AtomicAlbatross/esPass/Words.h

static const String wordList[] PROGMEM = {"Smoothly",
"Clearly",
"Strongly",
"Abnormally",
"Generously",
"Specifically",
"Upbeat",
"Scarcely",
"Fully",
"Frantically",
"Kindheartedly",
"Deftly",
"Grass",
"Stimulating",
"Thoughtful",
"Red",
"Elastic",
"Dare",
"Extra-large",
"Adhesive",
"Intelligent",
"Repeat",
"Voyage",
"Wall",
"Preserve",
"Territory",
"Story",
"Agonizing",
"Swing",
"Chunky",
"Waggish",
"Grubby",
"Cushion",
"Winter",
"Fowl",
"Shoes",
"Value",
"Airplane",
"Thread",
"Zipper",
"Mother",
"Quicksand",
"Roll",
"Legs",
"Treatment",
"Farm",
"Pocket",
"Yarn",
"Brake",
"Circle",
"Horn",
"Skate",
"Liquid",
"Join",
"Apparatus",
"Bomb",
"Zephyr",
"Price",
"Pot",
"Error",
"Hammer",
"Sheep",
"Roof",
"Memory",
"Minister",
"Jelly",
"Zebra",
"Cherry",
"Rice",
"Prose",
"Clam",
"Question",
"Desire",
"Aftermath",
"Adjustment",
"Cheese",
"Jellyfish",
"Seed",
"Push",
"Top",
"Record",
"Robin",
"Receipt",
"Rail",
"Stew",
"Stove",
"Act",
"Ants",
"Visitor",
"Pies",
"Note",
"Mint",
"Hydrant",
"Part",
"Attack",
"Beef",
"Middle",
"Steam",
"Lip",
"Shape",
"Money",
"Experience",
"Achiever",
"Lake",
"Scarf",
"Yam",
"Fire",
"Limit",
"Daughter",
"Night",
"Shake",
"Rain",
"Birth",
"Boot",
"Meeting",
"Believe",
"Flock",
"Animal",
"Design",
"Soda",
"Border",
"Writing",
"Statement",
"Servant",
"Rake",
"Laborer",
"Cow",
"Machine",
"Tongue",
"Apparel",
"Popcorn",
"Wrench",
"Turndown",
"Wheelbase",
"Wavelike",
"Backslap",
"Turnaround",
"Stoplight",
"Supermen",
"Bowlegs",
"Cheesecake",
"Supercargo",
"Goodnight",
"Timeshare",
"Playback",
"Bookworm",
"Overshoes",
"Turnaround",
"Sideshow",
"Scapegoat",
"Soybean",
"Railroad",
":",
"-",
"$",
"&",
"/",
"~",
"+",
"§",
"(",
")",
"!"};
